wdjose/3d-printed-biped-robot/3D Model/Hip DShaft B.SLDPRT

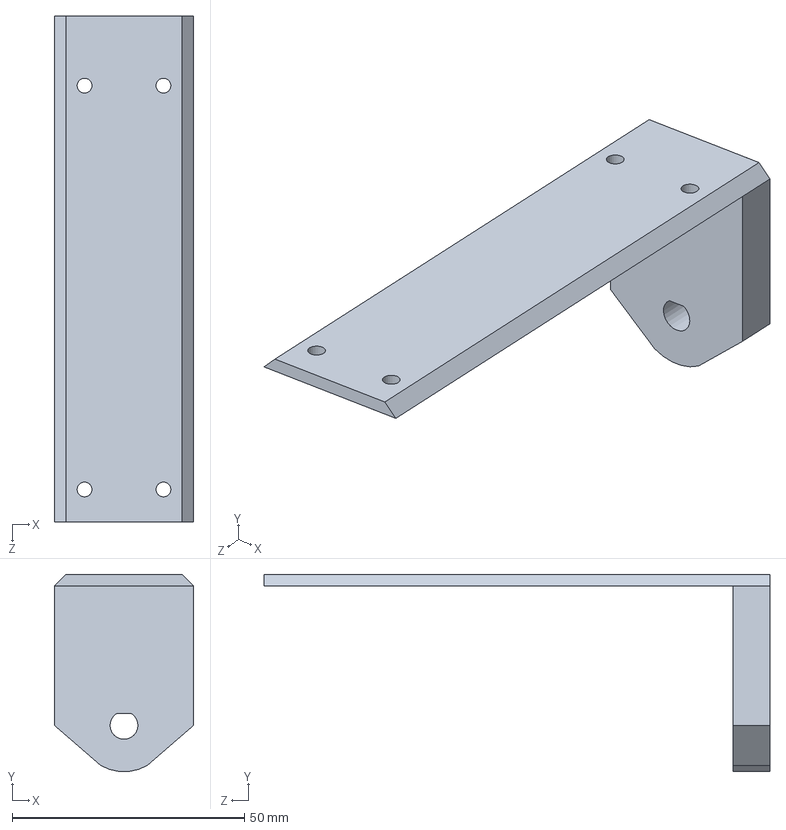
[picture p15: CAD file, 2018-08-21]
3D Model/Hip DShaft B.SLDPRT
30.0 x 42.4 x 109.0 mm
