wdjose/3d-printed-biped-robot/3D Model/Bearing Outer.SLDPRT

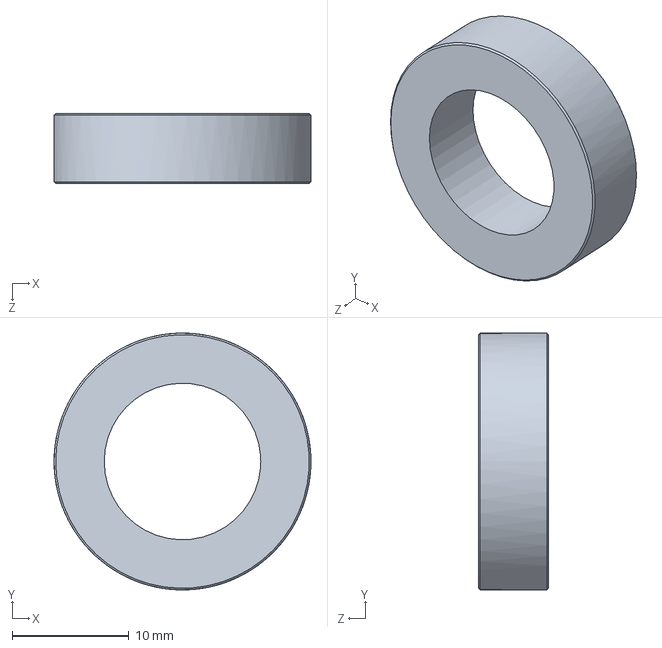
[picture p16: CAD file, 2018-08-21]
3D Model/Bearing Outer.SLDPRT
22.0 x 22.0 x 6.00 mm
