wdjose/3d-printed-biped-robot/3D Model/Hip Bearing A.SLDPRT

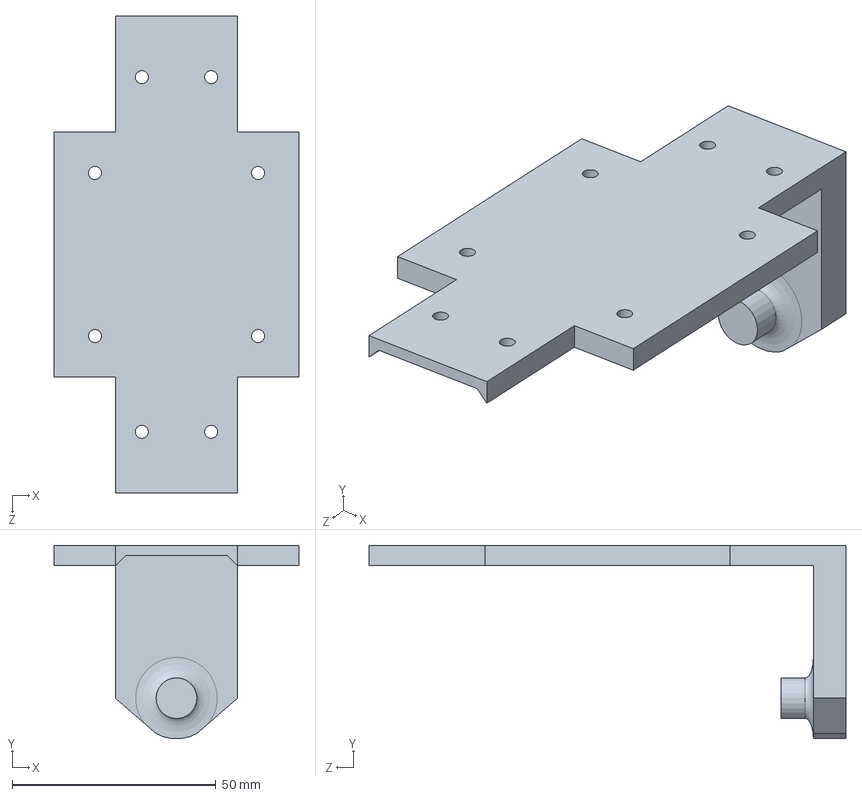
[picture p17: CAD file, 2018-08-21]
3D Model/Hip Bearing A.SLDPRT
60.0 x 47.4 x 117.0 mm
