wdjose/3d-printed-biped-robot/3D Model/Hip B.SLDPRT

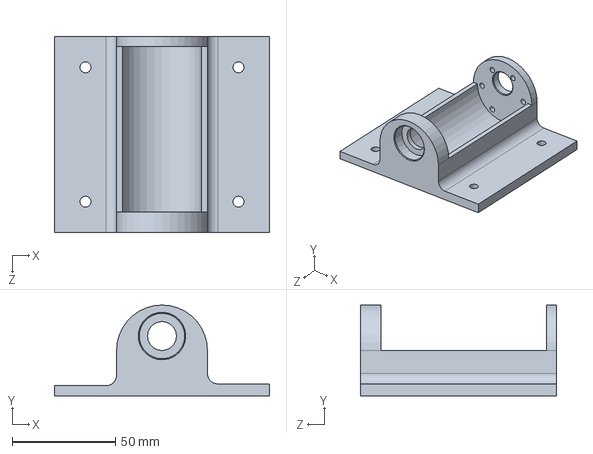
[picture p18: CAD file, 2018-08-21]
3D Model/Hip B.SLDPRT
104.0 x 44.0 x 95.0 mm
