wdjose/3d-printed-biped-robot/3D Model/Ankle DShaft.SLDPRT

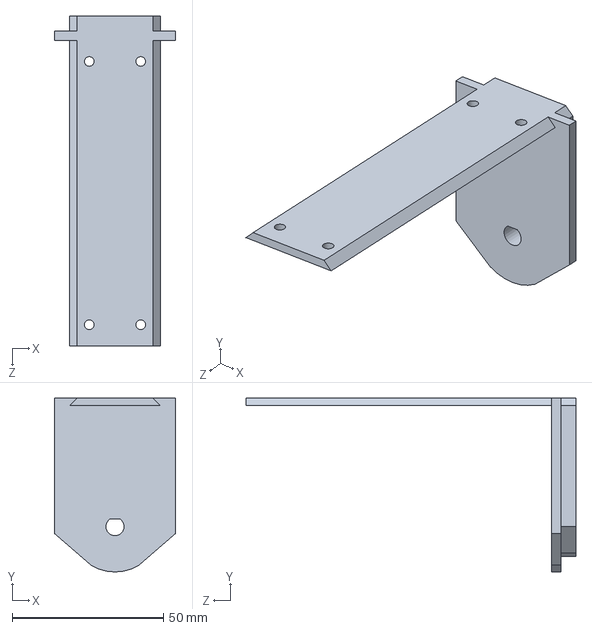
[picture p19: CAD file, 2018-08-21]
3D Model/Ankle DShaft.SLDPRT
40.0 x 57.5 x 109.0 mm
