wdjose/3d-printed-biped-robot/3D Model/Motor Gearbox.SLDPRT

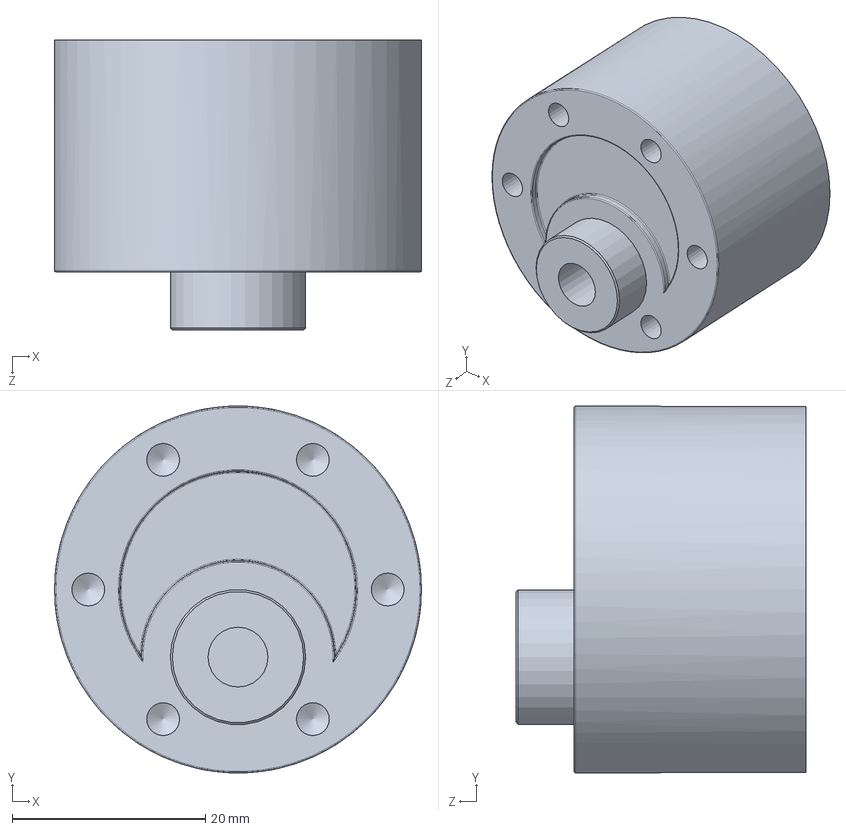
[picture p20: CAD file, 2018-08-21]
3D Model/Motor Gearbox.SLDPRT
38.0 x 38.0 x 30.0 mm
