wdjose/3d-printed-biped-robot/3D Model/Torso Base Reinforcement.SLDPRT

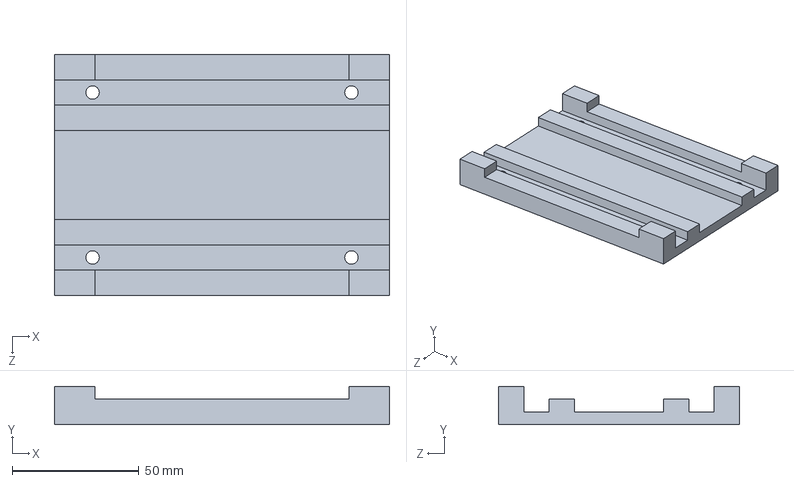
[picture p21: CAD file, 2018-08-21]
3D Model/Torso Base Reinforcement.SLDPRT
132.0 x 15.0 x 95.0 mm
