wdjose/3d-printed-biped-robot/3D Model/Motor Encoder.SLDPRT

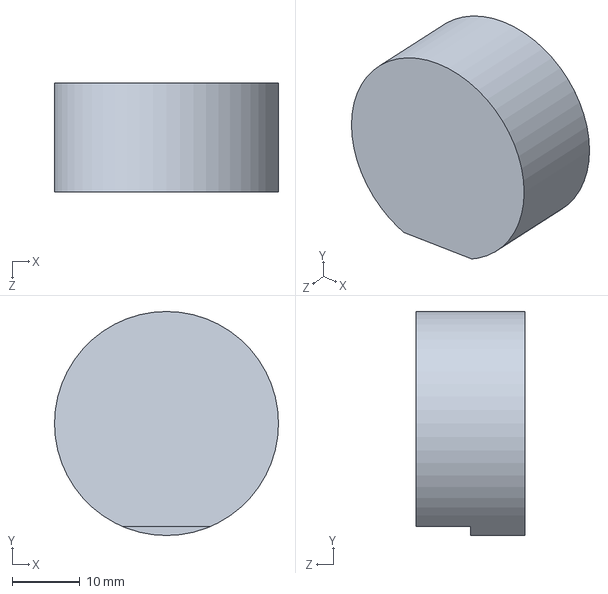
[picture p22: CAD file, 2018-08-21]
3D Model/Motor Encoder.SLDPRT
33.0 x 33.0 x 16.0 mm
