wdjose/3d-printed-biped-robot/3D Model/Bearing Inner.SLDPRT

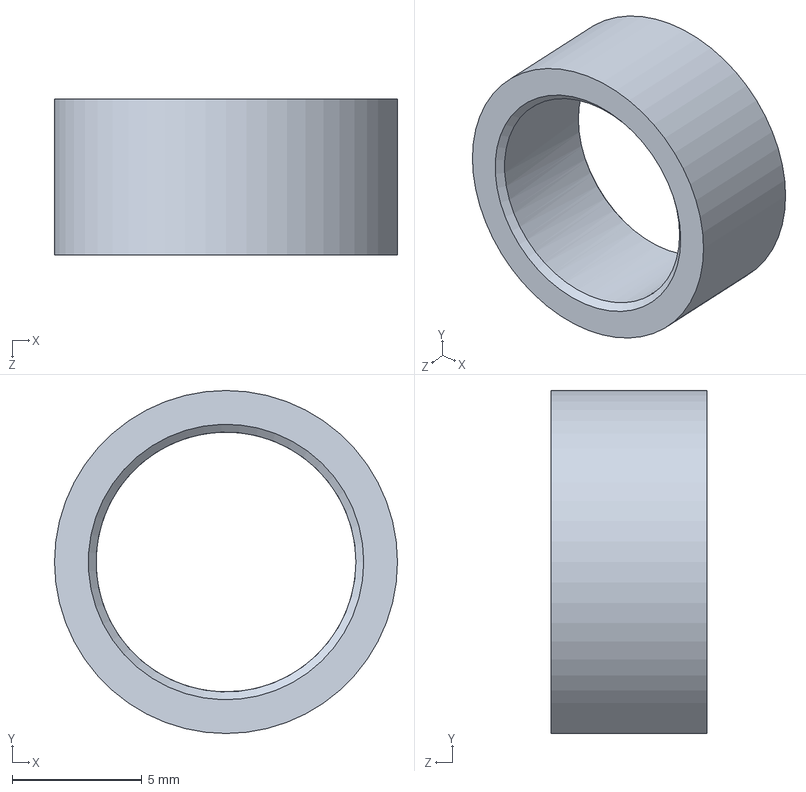
[picture p23: CAD file, 2018-08-21]
3D Model/Bearing Inner.SLDPRT
13.2 x 13.2 x 6.00 mm
