wdjose/3d-printed-biped-robot/Master Controller/motion.c

#include "init.h"

const int motion_len = 700;

const __prog__ int __attribute__((space(prog))) motion[][10] = {
	{0, 0, 0, 0, 0, 0, 0, 0, 0, 0},
	{0, 0, 0, 0, 0, 0, 0, 0, 0, 0},
	{0, 0, 0, 0, 0, 0, 0, 0, 0, 0},
	{0, 0, 0, 0, 0, 0, 0, 0, 0, 0},
	{0, 0, 0, 0, 0, 0, 0, 0, 0, 0},
	{0, 0, 0, 0, 0, 0, 0, 0, 0, 0},
	{0, 0, 0, 0, 0, 0, 0, 0, 0, 0},
	{0, 0, 0, 0, 0, 0, 0, 0, 0, 0},
	{0, 0, 0, 0, 0, 0, 0, 0, 0, 0},
	{0, 0, 0, 0, 0, 0, 0, 0, 0, 0},
	{0, 0, 0, 0, 0, 0, 0, 0, 0, 0},
	{0, 0, 0, 0, 0, 0, 0, 0, 0, 0},
	{0, 0, 0, 0, 0, 0, 0, 0, 0, 0},
	{0, 0, 0, 0, 0, 0, 0, 0, 0, 0},
	{0, 0, 0, 0, 0, 0, 0, 0, 0, 0},
	{0, 0, 0, 0, 0, 0, 0, 0, 0, 0},
	{0, 0, 0, 0, 0, 0, 0, 0, 0, 0},
	{0, 0, 0, 0, 0, 0, 0, 0, 0, 0},
	{0, 0, 0, 0, 0, 0, 0, 0, 0, 0},
	{0, 0, 0, 0, 0, 0, 0, 0, 0, 0},
	{0, 0, 0, 0, 0, 0, 0, 0, 0, 0},
	{0, 0, 0, 0, 0, 0, 0, 0, 0, 0},
	{0, 0, 0, 0, 0, 0, 0, 0, 0, 0},
	{0, 0, 0, 0, 0, 0, 0, 0, 0, 0},
	{0, 0, 0, 0, 0, 0, 0, 0, 0, 0},
	{0, 0, 0, 0, 0, 0, 0, 0, 0, 0},
	{0, 0, 0, 0, 0, 0, 0, 0, 0, 0},
	{0, 0, 0, 0, 0, 0, 0, 0, 0, 0},
	{0, 0, 0, 0, 0, 0, 0, 0, 0, 0},
	{0, 0, 0, 0, 0, 0, 0, 0, 0, 0},
	{0, 0, 0, 0, 0, 0, 0, 0, 0, 0},
	{0, 0, 0, 0, 0, 0, 0, 0, 0, 0},
	{0, 0, 0, 0, 0, 0, 0, 0, 0, 0},
	{0, 0, 0, 0, 0, 0, 0, 0, 0, 0},
	{0, 0, 0, 0, 0, 0, 0, 0, 0, 0},
	{0, 0, 0, 0, 0, 0, 0, 0, 0, 0},
	{0, 0, 0, 0, 0, 0, 0, 0, 0, 0},
	{0, 0, 0, 0, 0, 0, 0, 0, 0, 0},
	{0, 0, 0, 0, 0, 0, 0, 0, 0, 0},
	{0, 0, 0, 0, 0, 0, 0, 0, 0, 0},
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
};

const __prog__ int __attribute__((space(prog))) basetorque[][10] = {
	{0, 1365, 2154, -103, 0, 0, -1365, -2154, 103, 0},
	{0, 1365, 2154, -103, 0, 0, -1365, -2154, 103, 0},
	{0, 1365, 2154, -103, 0, 0, -1365, -2154, 103, 0},
	{0, 1365, 2154, -103, 0, 0, -1365, -2154, 103, 0},
	{0, 1365, 2154, -103, 0, 0, -1365, -2154, 103, 0},
	{0, 1365, 2154, -103, 0, 0, -1365, -2154, 103, 0},
	{0, 1365, 2154, -103, 0, 0, -1365, -2154, 103, 0},
	{0, 1365, 2154, -103, 0, 0, -1365, -2154, 103, 0},
	{0, 1365, 2154, -103, 0, 0, -1365, -2154, 103, 0},
	{0, 1365, 2154, -103, 0, 0, -1365, -2154, 103, 0},
	{0, 1365, 2154, -103, 0, 0, -1365, -2154, 103, 0},
	{0, 1365, 2154, -103, 0, 0, -1365, -2154, 103, 0},
	{0, 1365, 2154, -103, 0, 0, -1365, -2154, 103, 0},
	{0, 1365, 2154, -103, 0, 0, -1365, -2154, 103, 0},
	{0, 1365, 2154, -103, 0, 0, -1365, -2154, 103, 0},
	{0, 1365, 2154, -103, 0, 0, -1365, -2154, 103, 0},
	{0, 1365, 2154, -103, 0, 0, -1365, -2154, 103, 0},
	{0, 1365, 2154, -103, 0, 0, -1365, -2154, 103, 0},
	{0, 1365, 2154, -103, 0, 0, -1365, -2154, 103, 0},
	{0, 1365, 2154, -103, 0, 0, -1365, -2154, 103, 0},
	{0, 1365, 2154, -103, 0, 0, -1365, -2154, 103, 0},
	{0, 1365, 2154, -103, 0, 0, -1365, -2154, 103, 0},
	{0, 1365, 2154, -103, 0, 0, -1365, -2154, 103, 0},
	{0, 1365, 2154, -103, 0, 0, -1365, -2154, 103, 0},
	{0, 1365, 2154, -103, 0, 0, -1365, -2154, 103, 0},
	{0, 1365, 2154, -103, 0, 0, -1365, -2154, 103, 0},
	{0, 1365, 2154, -103, 0, 0, -1365, -2154, 103, 0},
	{0, 1365, 2154, -103, 0, 0, -1365, -2154, 103, 0},
	{0, 1365, 2154, -103, 0, 0, -1365, -2154, 103, 0},
	{0, 1365, 2154, -103, 0, 0, -1365, -2154, 103, 0},
	{0, 1365, 2154, -103, 0, 0, -1365, -2154, 103, 0},
	{0, 1365, 2154, -103, 0, 0, -1365, -2154, 103, 0},
	{0, 1365, 2154, -103, 0, 0, -1365, -2154, 103, 0},
	{0, 1365, 2154, -103, 0, 0, -1365, -2154, 103, 0},
	{0, 1365, 2154, -103, 0, 0, -1365, -2154, 103, 0},
	{0, 1365, 2154, -103, 0, 0, -1365, -2154, 103, 0},
	{0, 1365, 2154, -103, 0, 0, -1365, -2154, 103, 0},
	{0, 1365, 2154, -103, 0, 0, -1365, -2154, 103, 0},
	{0, 1365, 2154, -103, 0, 0, -1365, -2154, 103, 0},
	{0, 1365, 2154, -103, 0, 0, -1365, -2154, 103, 0},
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
};
